champal18/EDU-CIAA-PanelLed/Firmware/doc/uml/ciaaFirmware.png

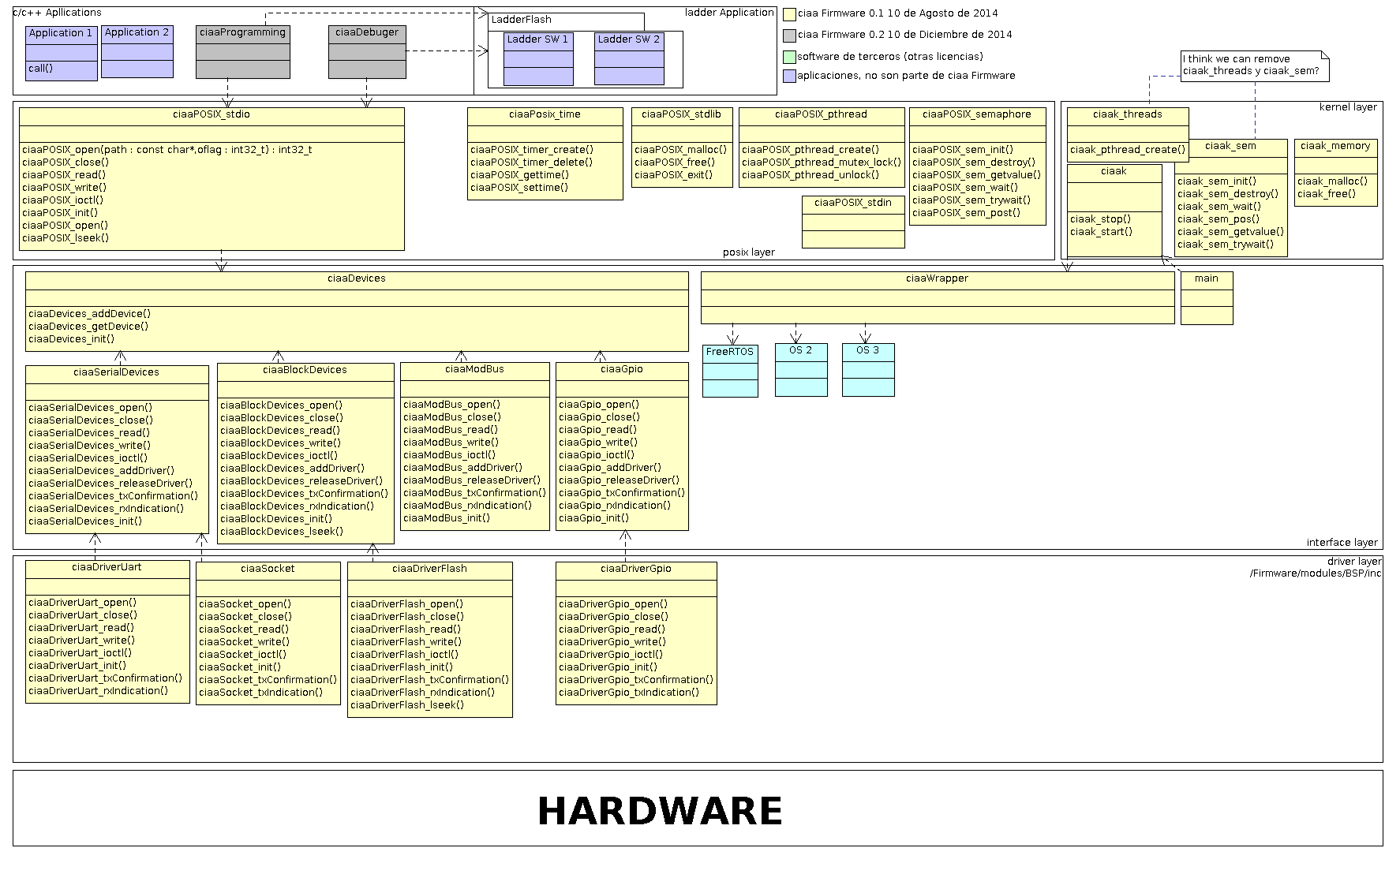
Firmware/doc/uml/ciaaFirmware.png
