champal18/EDU-CIAA-PanelLed/Firmware/doc/uml/open.png

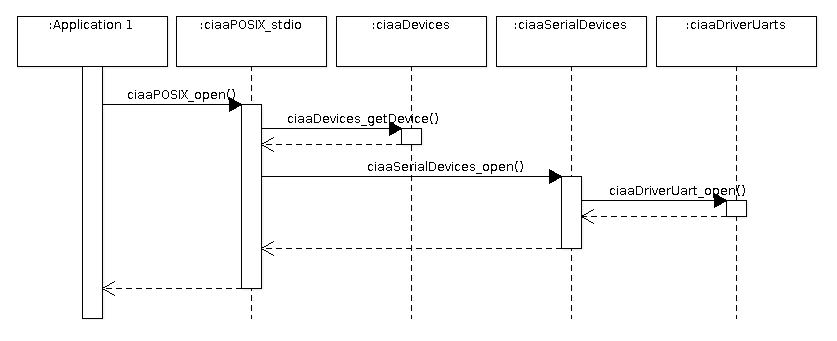
Firmware/doc/uml/open.png
