champal18/EDU-CIAA-PanelLed/Firmware/doc/uml/writenonblocking.png

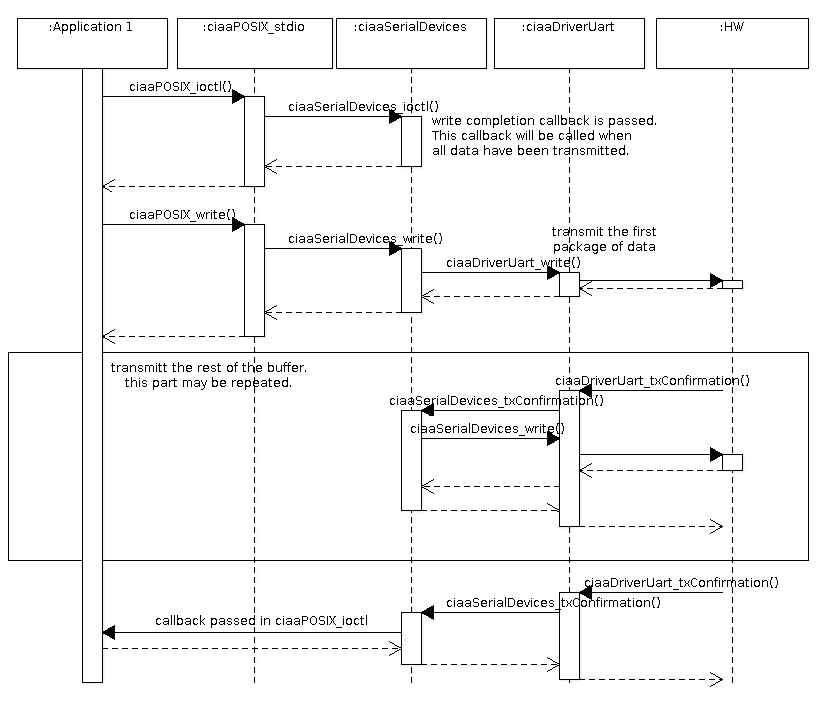
Firmware/doc/uml/writenonblocking.png
