champal18/EDU-CIAA-PanelLed/Firmware/projects/myproject/src/LedControl.c

/*==================[inclusions]=============================================*/

#include "LedControl.h"
#include "lcd.h"

/*==================[internal data declaration]==============================*/

// define max7219 registers
const uint8_t MAX7219_REG_NOOP        = 0;
const uint8_t MAX7219_REG_DIGIT0      = 1;
const uint8_t MAX7219_REG_DIGIT1      = 2;
const uint8_t MAX7219_REG_DIGIT2      = 3;
const uint8_t MAX7219_REG_DIGIT3      = 4;
const uint8_t MAX7219_REG_DIGIT4      = 5;
const uint8_t MAX7219_REG_DIGIT5      = 6;
const uint8_t MAX7219_REG_DIGIT6      = 7;
const uint8_t MAX7219_REG_DIGIT7      = 8;
const uint8_t MAX7219_REG_DECODEMODE  = 9;
const uint8_t MAX7219_REG_INTENSITY   = 10;
const uint8_t MAX7219_REG_SCANLIMIT   = 11;
const uint8_t MAX7219_REG_SHUTDOWN    = 12;
const uint8_t MAX7219_REG_DISPLAYTEST = 15;

uint8_t status[64];

uint8_t speed;
uint8_t intensity;
uint8_t mode;

extern uint8_t mensaje_actual[17];
extern uint8_t cursor;

/*==================[internal functions definition]==========================*/

void clearDisplay() 
{
	int i;
    for(i=0;i<8;i++)
    {
	   sendByte(i+1,0);
    }
}

void setRow(int row, uint8_t value)
{
    if(row<0 || row>7)
	   return;
    
    status[row]=value;
    sendByte(row+1,status[row]);
}

void printString(int pos, char string[]){
  
  int i=0;
  
  while (string[i] != '\0')
  {
    printChar(6*i+pos, string[i]);
    i++;
  }
  
}

void printStringScroll(int pos, char string[], int tDelay, char sentido)
{  
    int i=0, c=0; 
    while (string[c] != '\0')
    {
        c++;
    }

    if (sentido == '<')
    {  
        for (i=0; i<((c*6)+1); i++)
        {
          printString(-i+pos, string);
          LCD_delay_ms(tDelay);
        }
    }
    else    
        if (sentido == '>')
        {
            for (i=0; i<((c*6)+1); i++)
            {
              printString((-(c*6)+i)+pos, string);
              LCD_delay_ms(tDelay);
            }
        }
}

void sendByte(const uint8_t reg, const uint8_t data)
{
	uint8_t *buffer;
	int aux = (reg << 8) | data ;  // Buffer = 0000 0XXX (adress) 0000 0000 (data)
	buffer = &aux;
	Chip_SSP_WriteFrames_Blocking(LPC_SSP1, buffer, 1);	// Envio por SPP1

}	// end of sendByte

void printChar(int pos, char c)
{  
	uint8_t sRow[7];
	int i=0;

	sRow[0] = 0x00;
	sRow[6] = 0x00;

	switch (c){
	case ' ':
		sRow[1] = 0x00;
		sRow[2] = 0x00;
		sRow[3] = 0x00;
		sRow[4] = 0x00;
		sRow[5] = 0x00;
		break;

	case '!':
		sRow[1] = 0x00;
		sRow[2] = 0x00;
		sRow[3] = 0x2f;
		sRow[4] = 0x00;
		sRow[5] = 0x00;
		break;

	case '"':
		sRow[1] = 0x00;
		sRow[2] = 0x07;
		sRow[3] = 0x00;
		sRow[4] = 0x07;
		sRow[5] = 0x00;
		break;

	case '#':
		sRow[1] = 0x14;
		sRow[2] = 0x7f;
		sRow[3] = 0x14;
		sRow[4] = 0x7f;
		sRow[5] = 0x14;
		break;

	case '$':
		sRow[1] = 0x24;
		sRow[2] = 0x2a;
		sRow[3] = 0x7f;
		sRow[4] = 0x2a;
		sRow[5] = 0x12;
		break;

	case '%':
		sRow[1] = 0x62;
		sRow[2] = 0x64;
		sRow[3] = 0x08;
		sRow[4] = 0x13;
		sRow[5] = 0x23;
		break;

	case '&':
		sRow[1] = 0x36;
		sRow[2] = 0x49;
		sRow[3] = 0x55;
		sRow[4] = 0x22;
		sRow[5] = 0x50;
		break;

	case '(':
		sRow[1] = 0x00;
		sRow[2] = 0x1c;
		sRow[3] = 0x22;
		sRow[4] = 0x41;
		sRow[5] = 0x00;
		break;

	case ')':
		sRow[1] = 0x00;
		sRow[2] = 0x41;
		sRow[3] = 0x22;
		sRow[4] = 0x1c;
		sRow[5] = 0x00;
	break;

	case '*':
		sRow[1] = 0x14;
		sRow[2] = 0x08;
		sRow[3] = 0x3E;
		sRow[4] = 0x08;
		sRow[5] = 0x14;
	break;

	case '+':
		sRow[1] = 0x08;
		sRow[2] = 0x08;
		sRow[3] = 0x3E;
		sRow[4] = 0x08;
		sRow[5] = 0x08;
	break;

	case ',':
		sRow[1] = 0x00;
		sRow[2] = 0xA0;
		sRow[3] = 0x60;
		sRow[4] = 0x00;
		sRow[5] = 0x00;
	break;

	case '-':
		sRow[1] = 0x08;
		sRow[2] = 0x08;
		sRow[3] = 0x08;
		sRow[4] = 0x08;
		sRow[5] = 0x08;
	break;

	case '.':
		sRow[1] = 0x00;
		sRow[2] = 0x60;
		sRow[3] = 0x60;
		sRow[4] = 0x00;
		sRow[5] = 0x00;
	break;

	case '/':
		sRow[1] = 0x20;
		sRow[2] = 0x10;
		sRow[3] = 0x08;
		sRow[4] = 0x04;
		sRow[5] = 0x02;
	break;

	case '0':
		sRow[1] = 0x3E;
		sRow[2] = 0x51;
		sRow[3] = 0x49;
		sRow[4] = 0x45;
		sRow[5] = 0x3E;
	break;

	case '1':
		sRow[1] = 0x00;
		sRow[2] = 0x42;
		sRow[3] = 0x7F;
		sRow[4] = 0x40;
		sRow[5] = 0x00;
	break;

	case '2':
		sRow[1] = 0x42;
		sRow[2] = 0x61;
		sRow[3] = 0x51;
		sRow[4] = 0x49;
		sRow[5] = 0x46;
	break;

	case '3':
		sRow[1] = 0x21;
		sRow[2] = 0x41;
		sRow[3] = 0x45;
		sRow[4] = 0x4B;
		sRow[5] = 0x31;
	break;

	case '4':
		sRow[1] = 0x18;
		sRow[2] = 0x14;
		sRow[3] = 0x12;
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
		sRow[3] = 0x44;
		sRow[4] = 0x40;
		sRow[5] = 0x20;
	break;

	case 'u':
		sRow[1] = 0x3C;
		sRow[2] = 0x40;
		sRow[3] = 0x40;
		sRow[4] = 0x20;
		sRow[5] = 0x7C;
	break;

	case 'v':
		sRow[1] = 0x1C;
		sRow[2] = 0x20;
		sRow[3] = 0x40;
		sRow[4] = 0x20;
		sRow[5] = 0x1C;
	break;

	case 'w':
		sRow[1] = 0x3C;
		sRow[2] = 0x40;
		sRow[3] = 0x30;
		sRow[4] = 0x40;
		sRow[5] = 0x3C;
	break;

	case 'x':
		sRow[1] = 0x44;
		sRow[2] = 0x28;
		sRow[3] = 0x10;
		sRow[4] = 0x28;
		sRow[5] = 0x44;
	break;

	case 'y':
		sRow[1] = 0x1C;
		sRow[2] = 0xA0;
		sRow[3] = 0xA0;
		sRow[4] = 0xA0;
		sRow[5] = 0x7C;
	break;

	case 'z':
		sRow[1] = 0x44;
		sRow[2] = 0x64;
		sRow[3] = 0x54;
		sRow[4] = 0x4C;
		sRow[5] = 0x44;
	break;

	case '{':
		sRow[1] = 0x00;
		sRow[2] = 0x10;
		sRow[3] = 0x7C;
		sRow[4] = 0x82;
		sRow[5] = 0x00;
	break;

	case '|':
		sRow[1] = 0x00;
		sRow[2] = 0x00;
		sRow[3] = 0xFF;
		sRow[4] = 0x00;
		sRow[5] = 0x00;
	break;

	case '}':
		sRow[1] = 0x00;
		sRow[2] = 0x82;
		sRow[3] = 0x7C;
		sRow[4] = 0x10;
		sRow[5] = 0x00;
	break;

	case 'º':
		sRow[1] = 0x00;
		sRow[2] = 0x06;
		sRow[3] = 0x09;
		sRow[4] = 0x09;
		sRow[5] = 0x06;
	break;
	}

	for (i=0; i<7; i++)
	{
	setRow(pos+i, sRow[i]);
	}

}

/*==================[external functions definition]==========================*/

// Setup del MAX7219
void Init_MAX7219(void)
{
	int i;
	for(i=1;i<65;i++)
		status[i]=0x00;
	sendByte (MAX7219_REG_DISPLAYTEST, 0); // no display test
	sendByte (MAX7219_REG_SCANLIMIT, 7);   // show all 8 digits
	sendByte (MAX7219_REG_DECODEMODE, 0);  // using an led matrix (not digits)
	clearDisplay();
	sendByte (MAX7219_REG_SHUTDOWN, 0);   // not in shutdown mode (ie. start it up)
	sendByte (MAX7219_REG_SHUTDOWN, 1);   // not in shutdown mode (ie. start it up)
	sendByte (MAX7219_REG_INTENSITY, intensity*3);  // character intensity: range: 0 to 15
	clearDisplay();

}	// end of Init_MAX7219

void msjScroll()
{
	int i = 0;

	int velocidad;
	switch(speed)
	{
		case 1:
		{
			velocidad = 200;
			break;
		}
		case 2:
		{
			velocidad = 185;
			break;
		}
		case 3:
		{
			velocidad = 170;
			break;
		}
		case 4:
		{
			velocidad = 155;
			break;
		}
		case 5:
		{
			velocidad = 140;
			break;
		}
		default:
		{
			velocidad = 170;
			break;
		}
	}

	switch(mode)
	{
		case 1:
		{
			int c = 0;
			while (mensaje_actual[c] != '\0')
			{
				c++;
			}
			for(i=0;i<c;i++)
			{
				clearDisplay();
				printChar(2,mensaje_actual[i]);
				LCD_delay_ms(velocidad*4);
			}
			break;
		}
		case 2:
		{
			clearDisplay();     //borrar pantalla '0'
			printStringScroll(1, mensaje_actual, velocidad, '<');
			LCD_delay_ms(250);
			clearDisplay();     //borrar pantalla '0'
			break;
		}
		case 3:
		{
			clearDisplay();     //borrar pantalla '0'
			printStringScroll(1, mensaje_actual, velocidad, '<');
			LCD_delay_ms(250);
			printStringScroll(1, mensaje_actual, velocidad, '>');
			LCD_delay_ms(250);
			clearDisplay();     //borrar pantalla '0'
			break;
		}
	}
}
